civilizayden/Christmas-light-show-/Christmas Can Can/Santa Sleigh-SNOW.gif

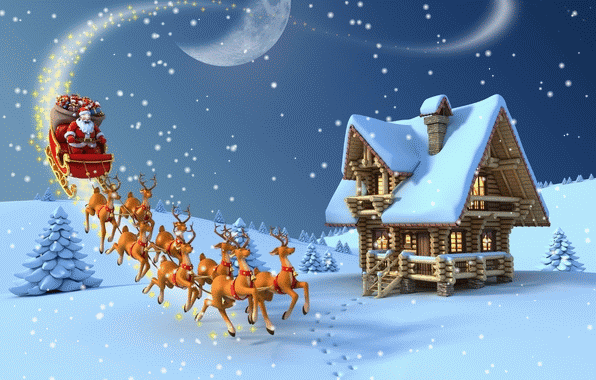
Christmas Can Can/Santa Sleigh-SNOW.gif
