civilizayden/Christmas-light-show-/Christmas Can Can/santa-claus-gif.gif

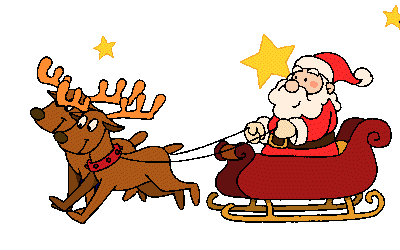
Christmas Can Can/santa-claus-gif.gif
