civilizayden/Christmas-light-show-/Christmas Every Day/Media/Cal.gif

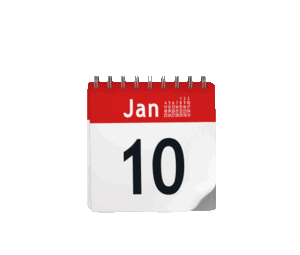
Christmas Every Day/Media/Cal.gif
