civilizayden/Christmas-light-show-/Christmas Every Day/Media/Caroler.gif

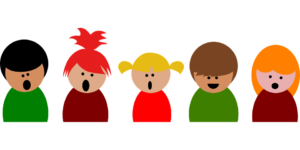
Christmas Every Day/Media/Caroler.gif
