civilizayden/Christmas-light-show-/Christmas Every Day/Media/Fireplace.jpg

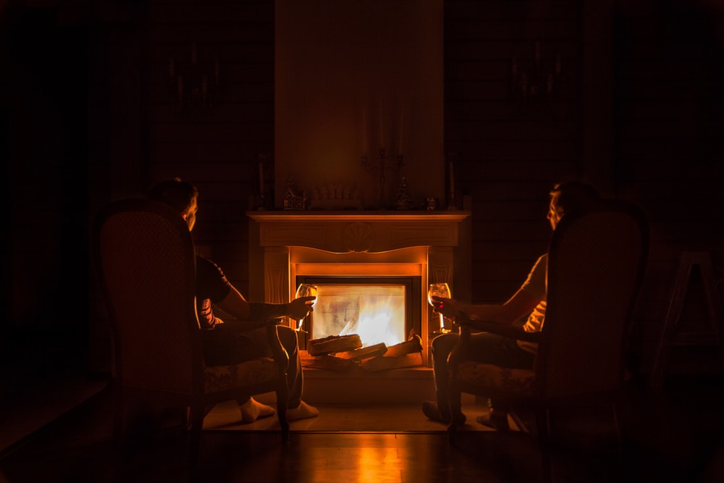
Christmas Every Day/Media/Fireplace.jpg
