civilizayden/Christmas-light-show-/Christmas Every Day/Media/Joy.png

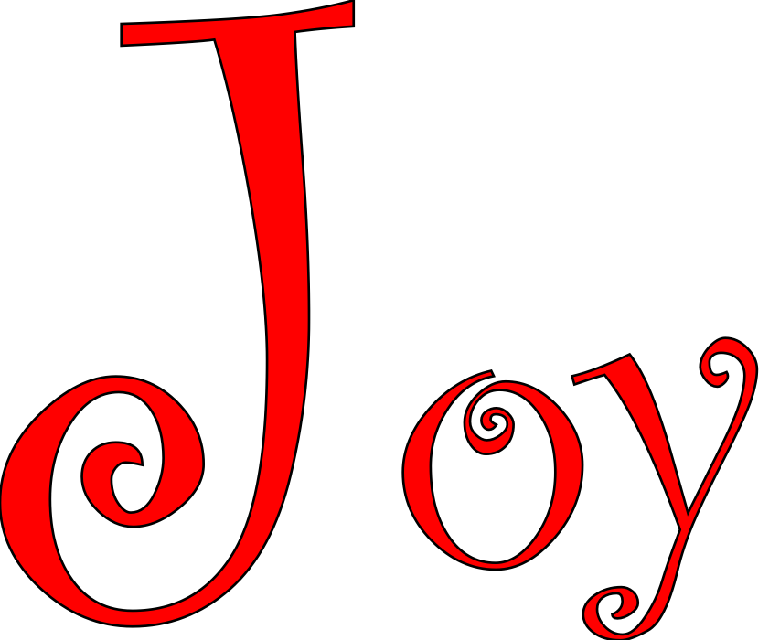
Christmas Every Day/Media/Joy.png
