civilizayden/Christmas-light-show-/Christmas Every Day/Media/MerryChristmas.png

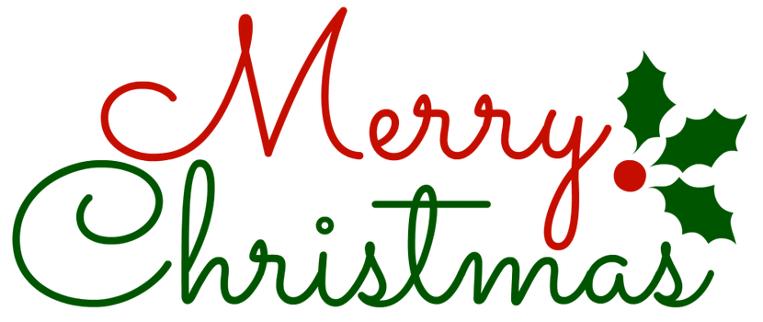
Christmas Every Day/Media/MerryChristmas.png
