civilizayden/Christmas-light-show-/Christmas Every Day/Media/presents.gif

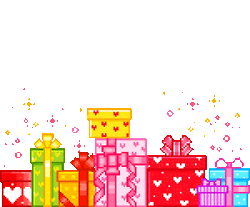
Christmas Every Day/Media/presents.gif
