civilizayden/Christmas-light-show-/Christmas Every Day/Media/Reindeer1.gif

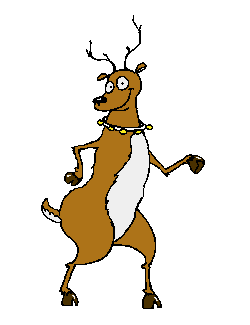
Christmas Every Day/Media/Reindeer1.gif
