civilizayden/Christmas-light-show-/Christmas Every Day/Media/Reindeer3.gif

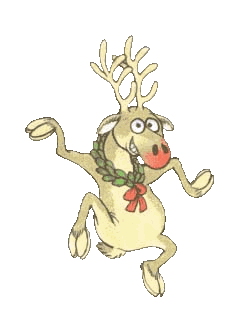
Christmas Every Day/Media/Reindeer3.gif
