civilizayden/Christmas-light-show-/Christmas Every Day/Media/Santa trumpet.gif

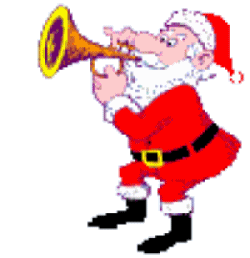
Christmas Every Day/Media/Santa trumpet.gif
