civilizayden/Christmas-light-show-/Christmas Every Day/Media/Sleep.gif

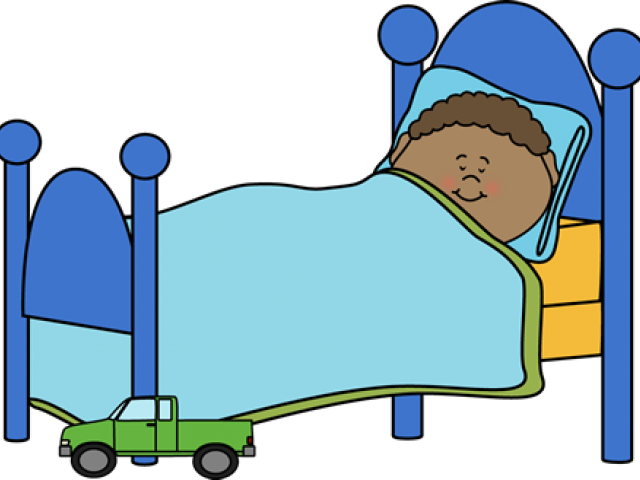
Christmas Every Day/Media/Sleep.gif
