civilizayden/Christmas-light-show-/Elf Song/The-Elf-Song/Traditional Layout/Angry Elf.png

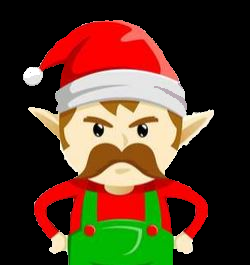
Elf Song/The-Elf-Song/Traditional Layout/Angry Elf.png
