civilizayden/Christmas-light-show-/Elf Song/The-Elf-Song/Traditional Layout/C.png

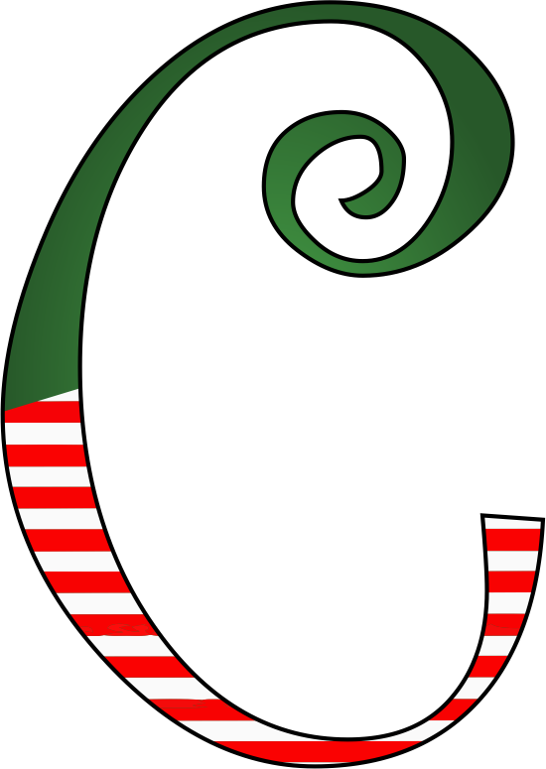
Elf Song/The-Elf-Song/Traditional Layout/C.png
