civilizayden/Christmas-light-show-/Elf Song/The-Elf-Song/Traditional Layout/Cookie.png

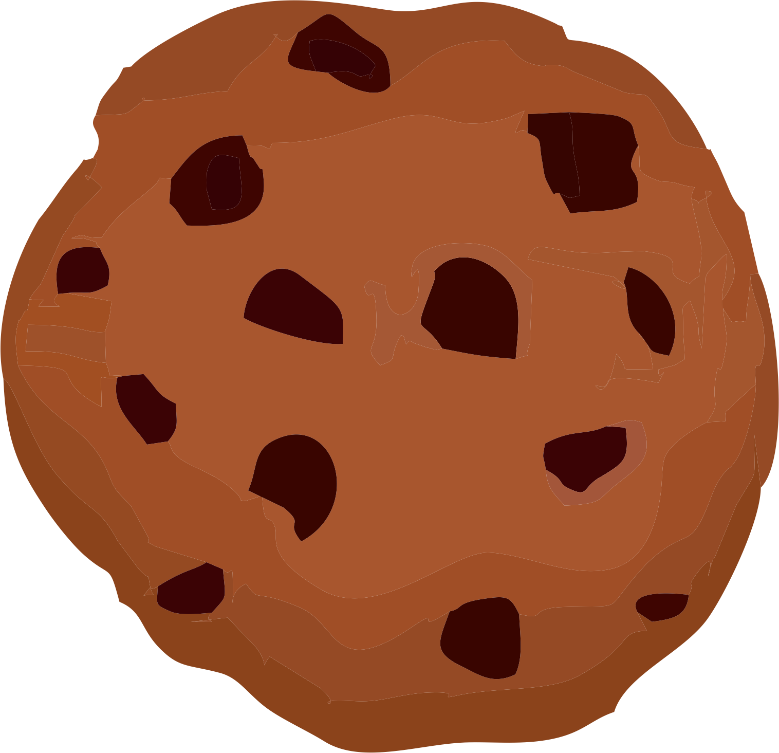
Elf Song/The-Elf-Song/Traditional Layout/Cookie.png
