civilizayden/Christmas-light-show-/Elf Song/The-Elf-Song/Traditional Layout/Dollar Bill.png

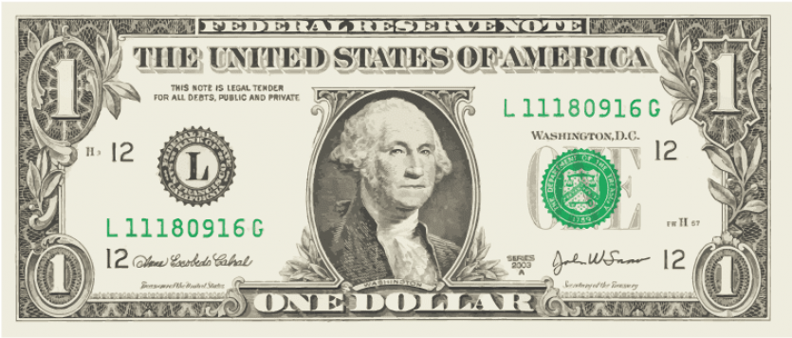
Elf Song/The-Elf-Song/Traditional Layout/Dollar Bill.png
