civilizayden/Christmas-light-show-/Elf Song/The-Elf-Song/Traditional Layout/E.png

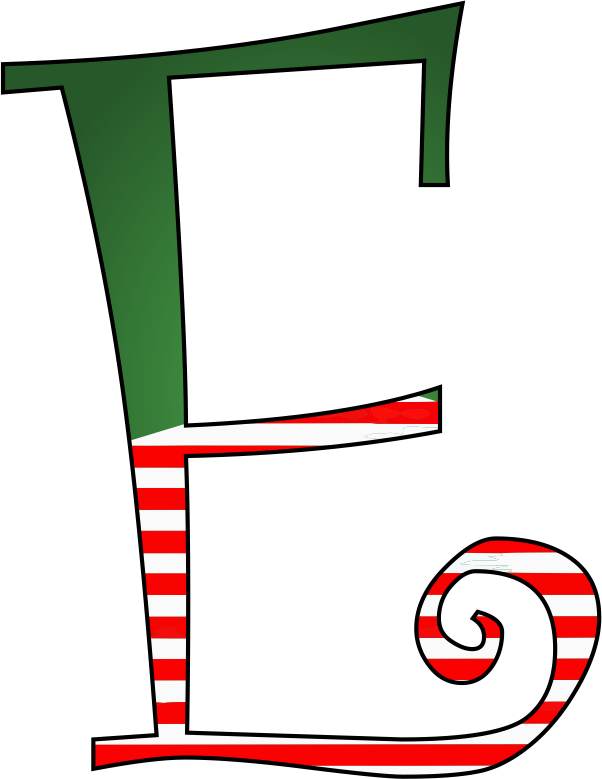
Elf Song/The-Elf-Song/Traditional Layout/E.png
