civilizayden/Christmas-light-show-/Elf Song/The-Elf-Song/Traditional Layout/Elf9.png

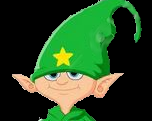
Elf Song/The-Elf-Song/Traditional Layout/Elf9.png
