civilizayden/Christmas-light-show-/Elf Song/The-Elf-Song/Traditional Layout/Elf9A.png

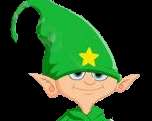
Elf Song/The-Elf-Song/Traditional Layout/Elf9A.png
