civilizayden/Christmas-light-show-/Elf Song/The-Elf-Song/Traditional Layout/Elf10.png

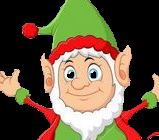
Elf Song/The-Elf-Song/Traditional Layout/Elf10.png
