civilizayden/Christmas-light-show-/Elf Song/The-Elf-Song/Traditional Layout/Elf10A.png

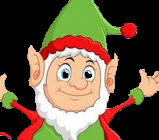
Elf Song/The-Elf-Song/Traditional Layout/Elf10A.png
