civilizayden/Christmas-light-show-/Elf Song/The-Elf-Song/Traditional Layout/Elf13.png

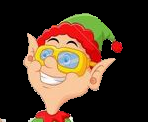
Elf Song/The-Elf-Song/Traditional Layout/Elf13.png
