civilizayden/Christmas-light-show-/Elf Song/The-Elf-Song/Traditional Layout/Elf13A.png

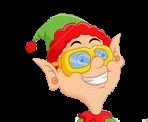
Elf Song/The-Elf-Song/Traditional Layout/Elf13A.png
