civilizayden/Christmas-light-show-/Elf Song/The-Elf-Song/Traditional Layout/Elf19.png

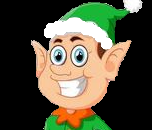
Elf Song/The-Elf-Song/Traditional Layout/Elf19.png
