civilizayden/Christmas-light-show-/Elf Song/The-Elf-Song/Traditional Layout/Elf20.png

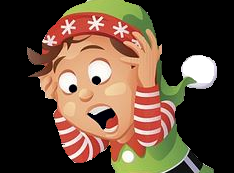
Elf Song/The-Elf-Song/Traditional Layout/Elf20.png
