civilizayden/Christmas-light-show-/Elf Song/The-Elf-Song/Traditional Layout/Elf.png

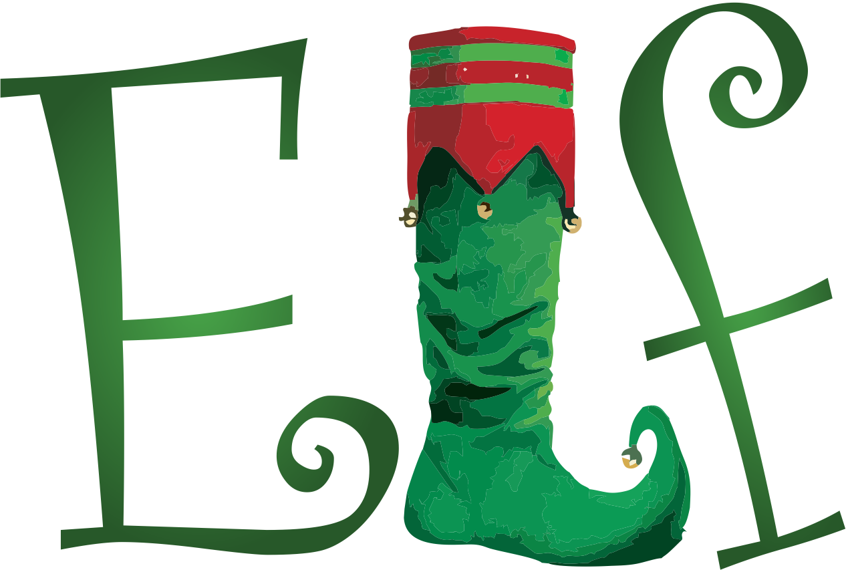
Elf Song/The-Elf-Song/Traditional Layout/Elf.png
