civilizayden/Christmas-light-show-/Elf Song/The-Elf-Song/Traditional Layout/Elf_AI_eo.png

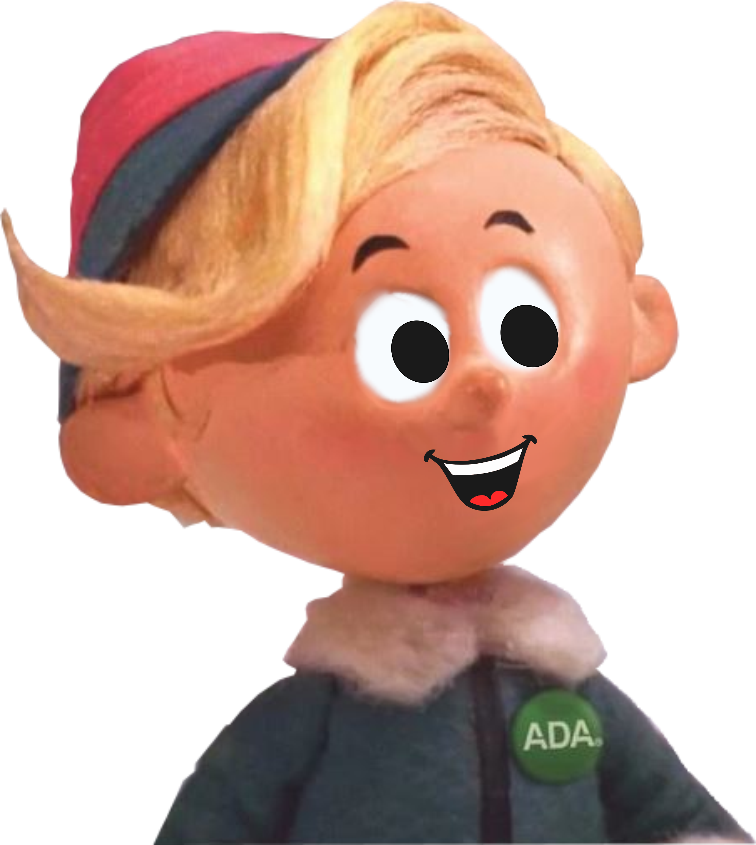
Elf Song/The-Elf-Song/Traditional Layout/Elf_AI_eo.png
