civilizayden/Christmas-light-show-/Elf Song/The-Elf-Song/Traditional Layout/High Five Santa.png

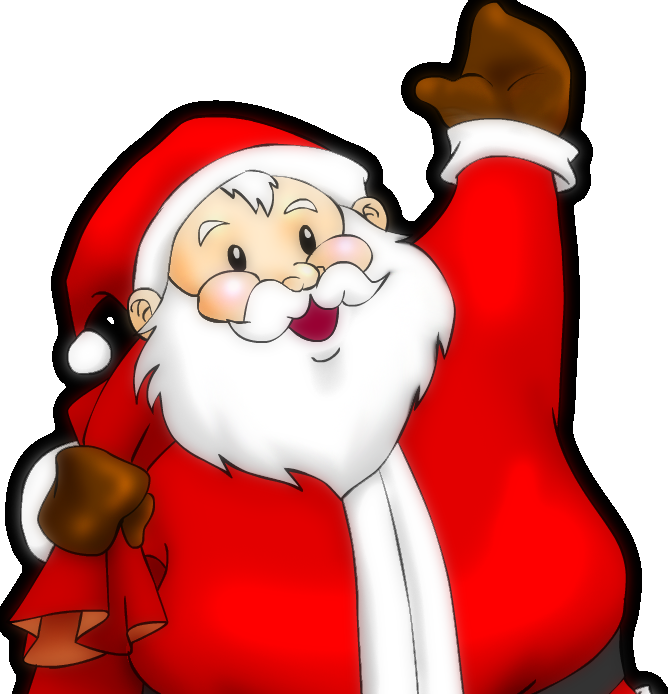
Elf Song/The-Elf-Song/Traditional Layout/High Five Santa.png
