civilizayden/Christmas-light-show-/Elf Song/The-Elf-Song/Traditional Layout/M and M Wages.png

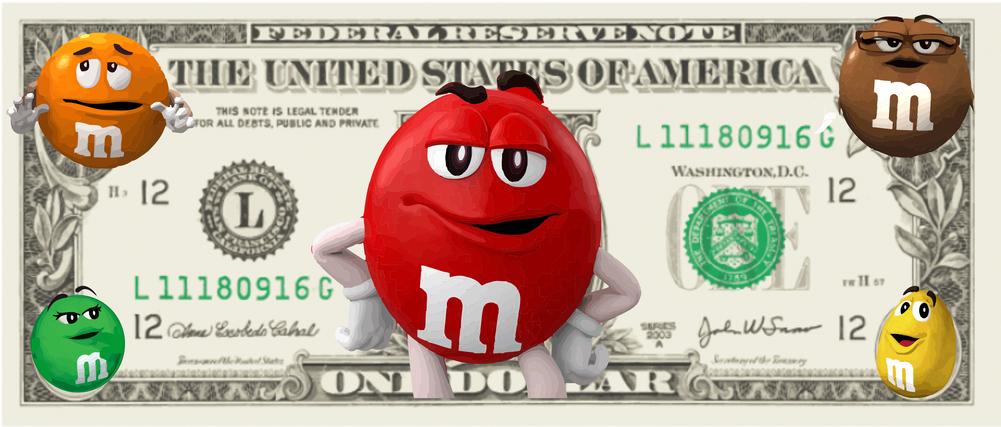
Elf Song/The-Elf-Song/Traditional Layout/M and M Wages.png
