civilizayden/Christmas-light-show-/Elf Song/The-Elf-Song/Traditional Layout/New Broad.PNG

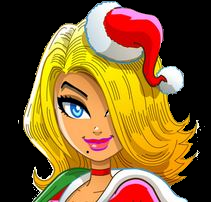
Elf Song/The-Elf-Song/Traditional Layout/New Broad.PNG
