civilizayden/Christmas-light-show-/Elf Song/The-Elf-Song/Traditional Layout/P.png

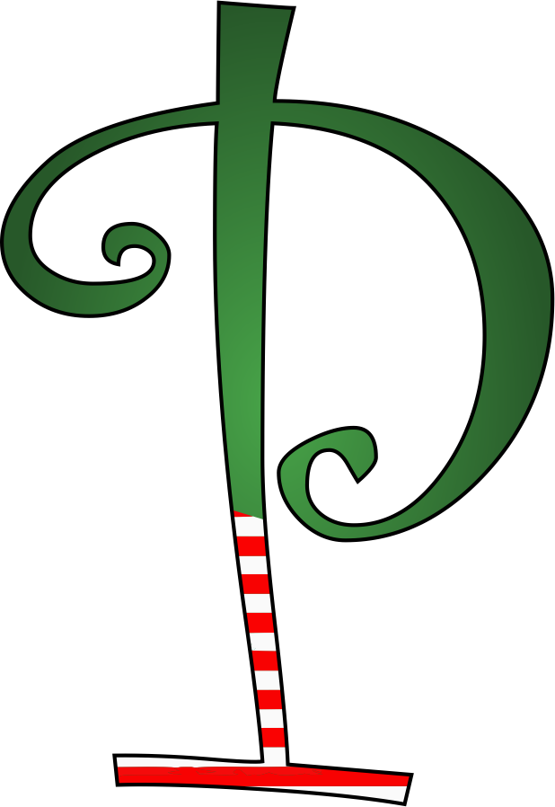
Elf Song/The-Elf-Song/Traditional Layout/P.png
