civilizayden/Christmas-light-show-/Elf Song/The-Elf-Song/Traditional Layout/Pointy Shoe Left.png

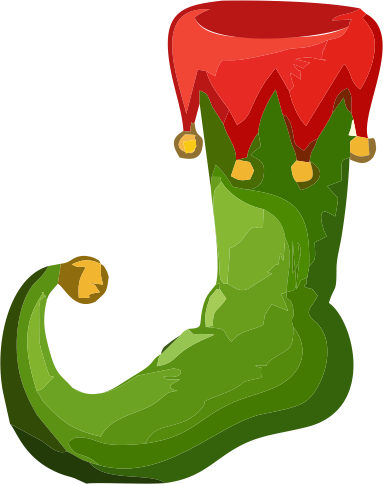
Elf Song/The-Elf-Song/Traditional Layout/Pointy Shoe Left.png
