civilizayden/Christmas-light-show-/Elf Song/The-Elf-Song/Traditional Layout/Pointy Shoe Right.png

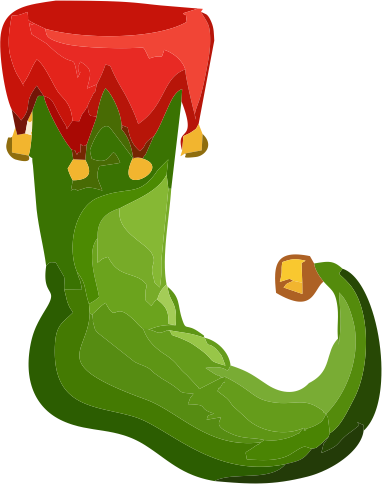
Elf Song/The-Elf-Song/Traditional Layout/Pointy Shoe Right.png
