civilizayden/Christmas-light-show-/Elf Song/The-Elf-Song/Traditional Layout/Pointy Shoes.png

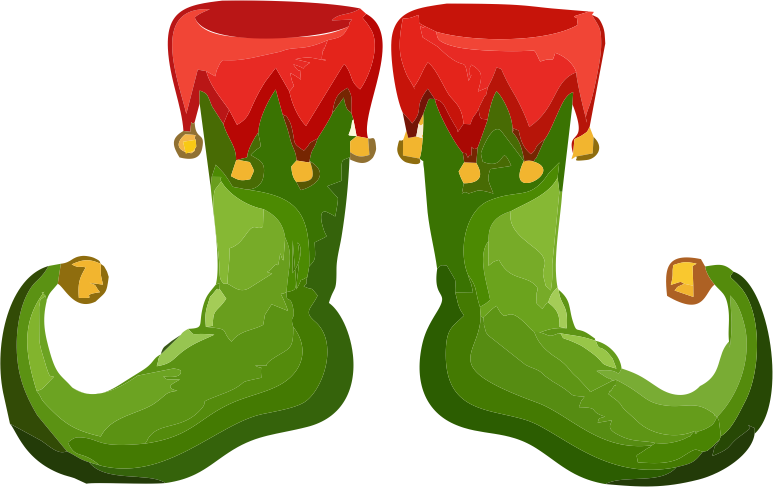
Elf Song/The-Elf-Song/Traditional Layout/Pointy Shoes.png
