civilizayden/Christmas-light-show-/Elf Song/The-Elf-Song/Traditional Layout/R.png

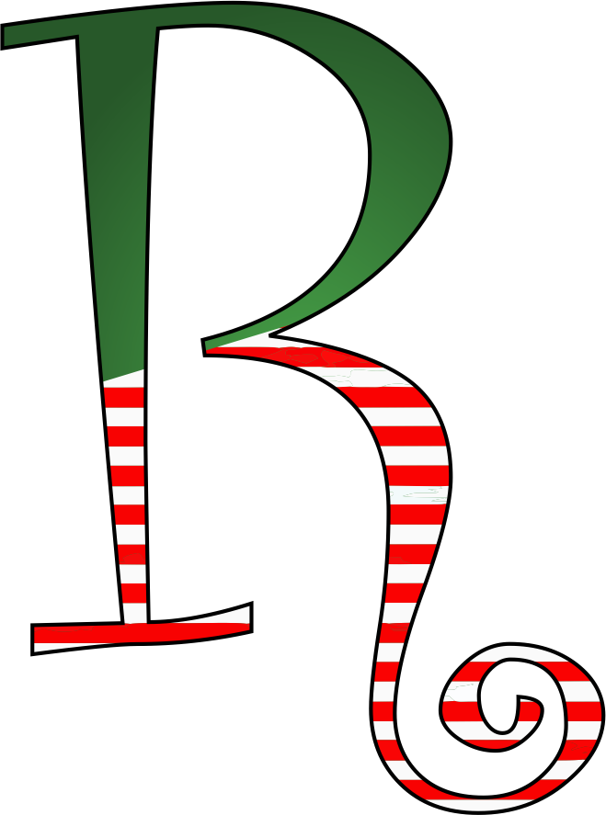
Elf Song/The-Elf-Song/Traditional Layout/R.png
