civilizayden/Christmas-light-show-/Elf Song/The-Elf-Song/Traditional Layout/S.png

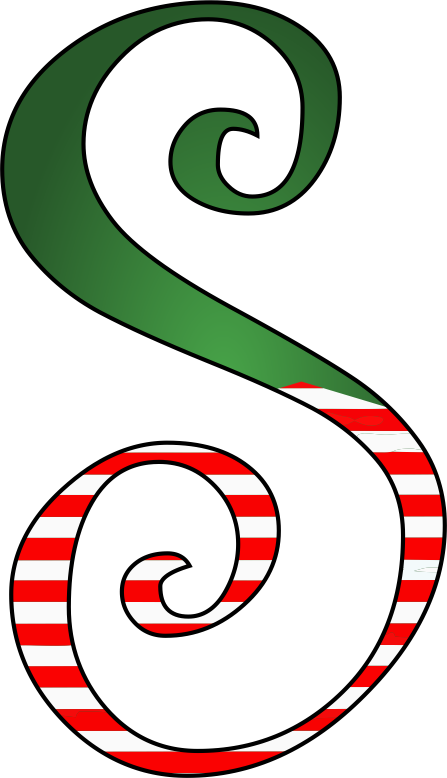
Elf Song/The-Elf-Song/Traditional Layout/S.png
