civilizayden/Christmas-light-show-/Elf Song/The-Elf-Song/Traditional Layout/Short Elf.png

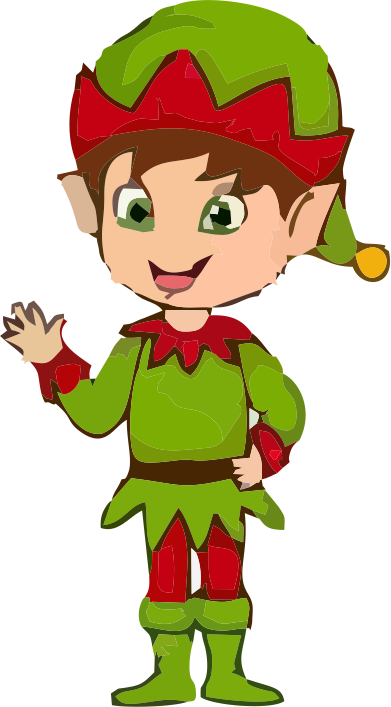
Elf Song/The-Elf-Song/Traditional Layout/Short Elf.png
