civilizayden/Christmas-light-show-/Elf Song/The-Elf-Song/Traditional Layout/T.png

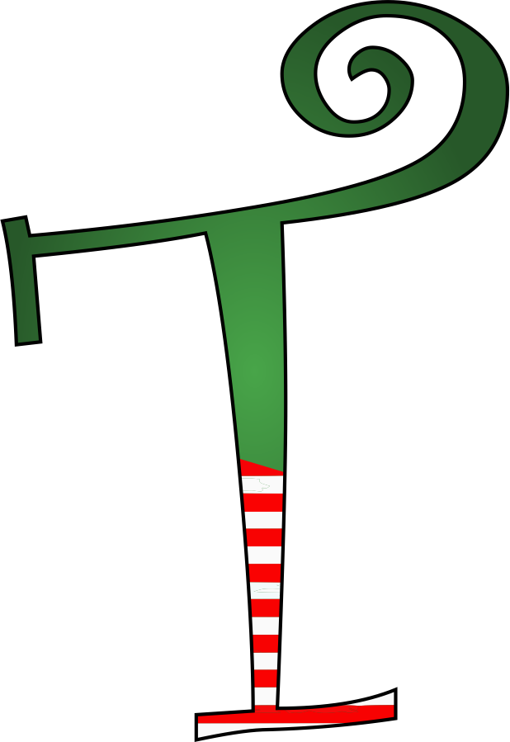
Elf Song/The-Elf-Song/Traditional Layout/T.png
