civilizayden/Christmas-light-show-/Layout and Xlights config/Images/DJI_0012.JPG

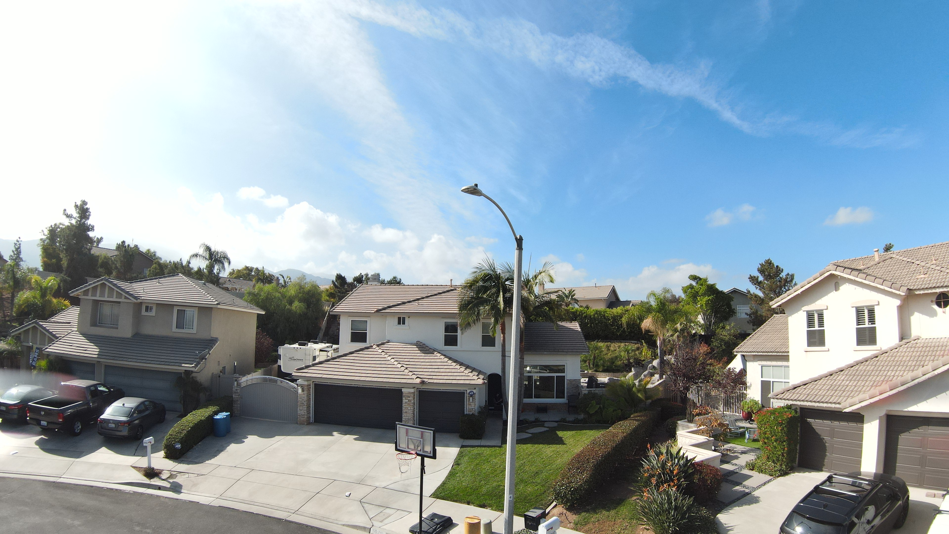
Layout and Xlights config/Images/DJI_0012.JPG
